FelipeToledo/DIY-SunPhotometer-UChile/manual_tex_files/Figuras/7.png

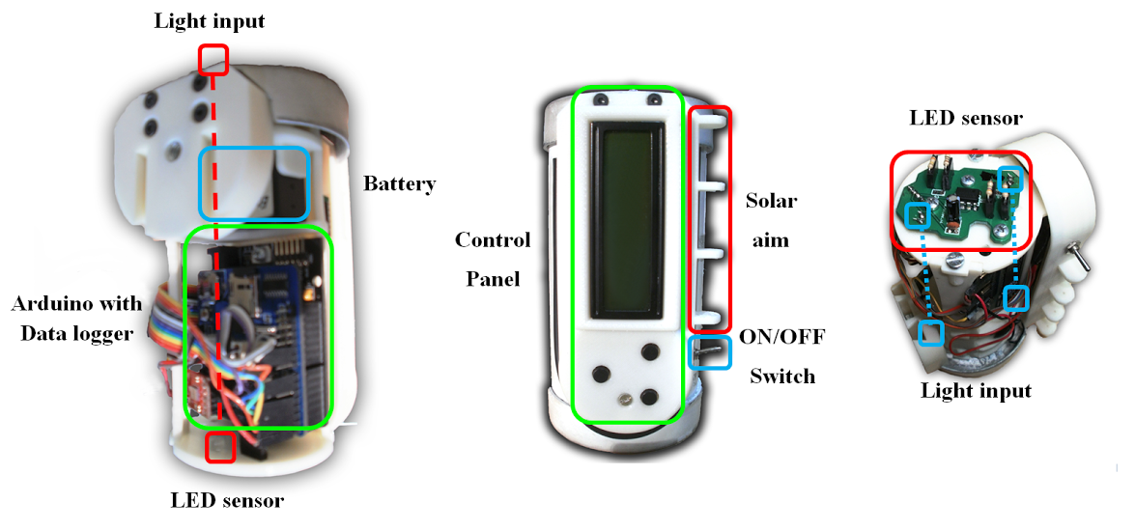
manual_tex_files/Figuras/7.png
